sparkletron/righteous_tentacle_colecovision/pics/signals/analog/Q3_collector_at_idle_no_game.png

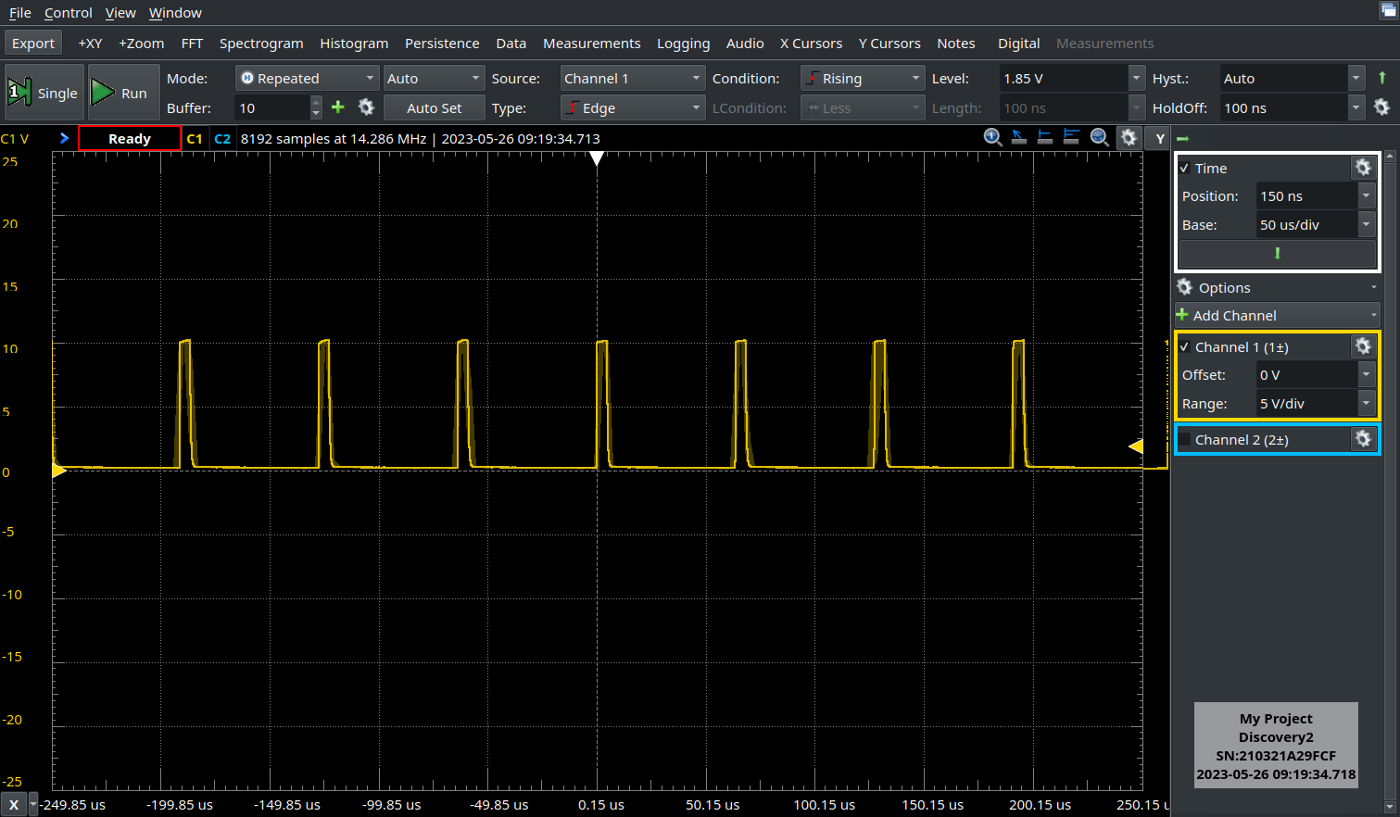
pics/signals/analog/Q3_collector_at_idle_no_game.png
