sparkletron/righteous_tentacle_colecovision/pics/signals/analog/rf_2_ac_at_idle_no_game.png

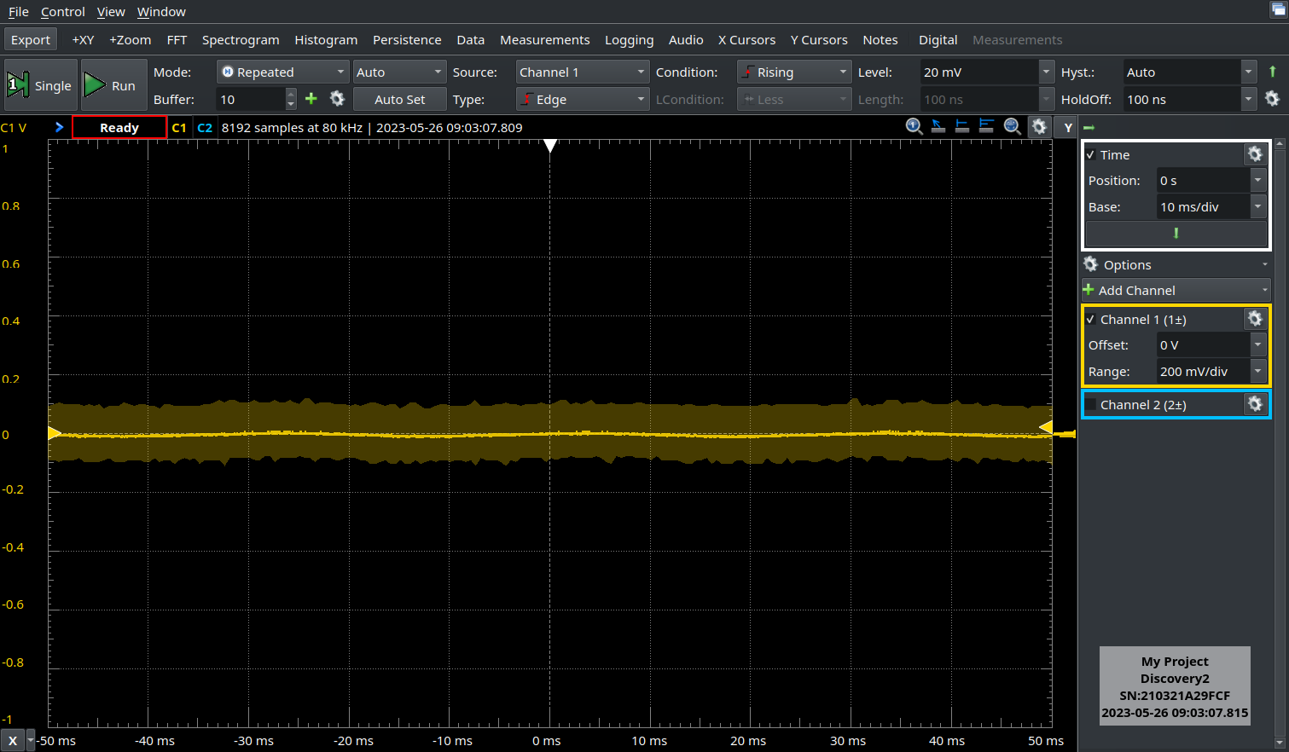
pics/signals/analog/rf_2_ac_at_idle_no_game.png
