sparkletron/righteous_tentacle_colecovision/pics/signals/analog/rf_7_Yb_ac_at_idle_no_game.png

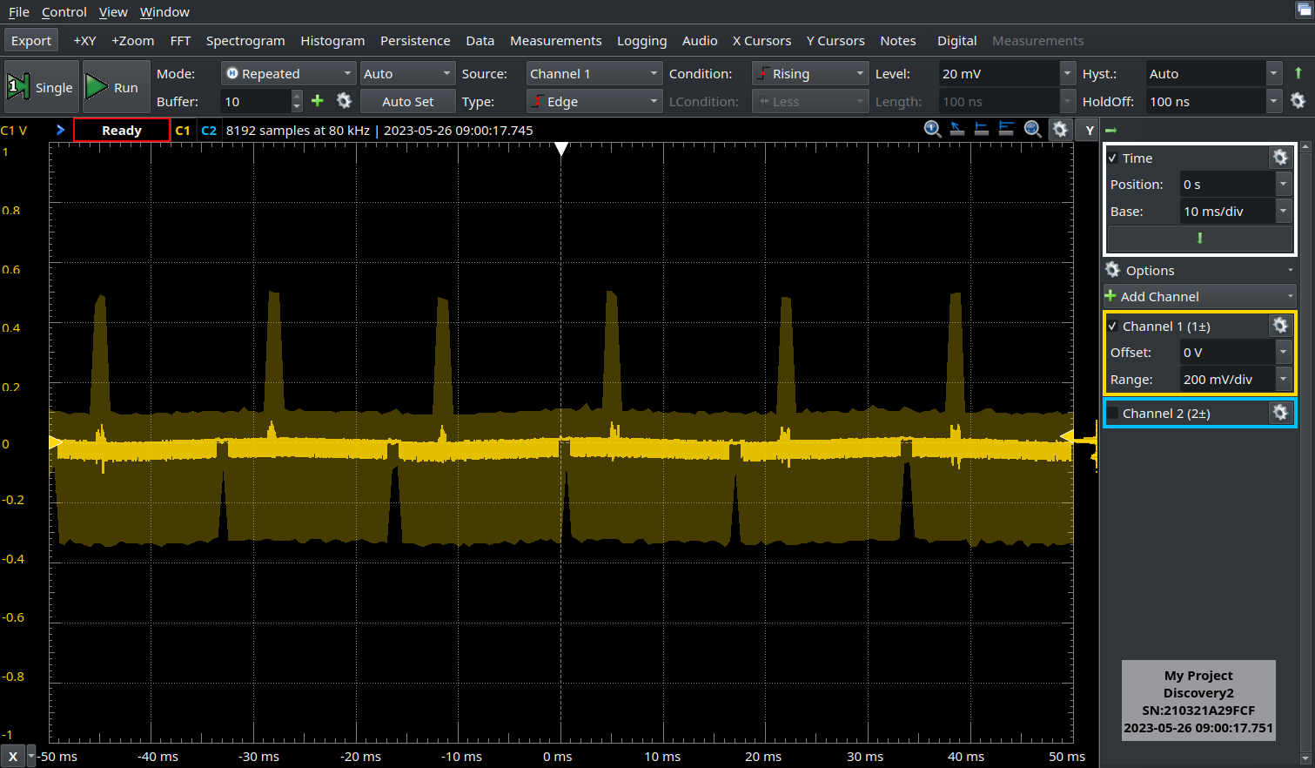
pics/signals/analog/rf_7_Yb_ac_at_idle_no_game.png
