sparkletron/righteous_tentacle_colecovision/pics/signals/analog/u7_1_A1_at_idle_no_game.png

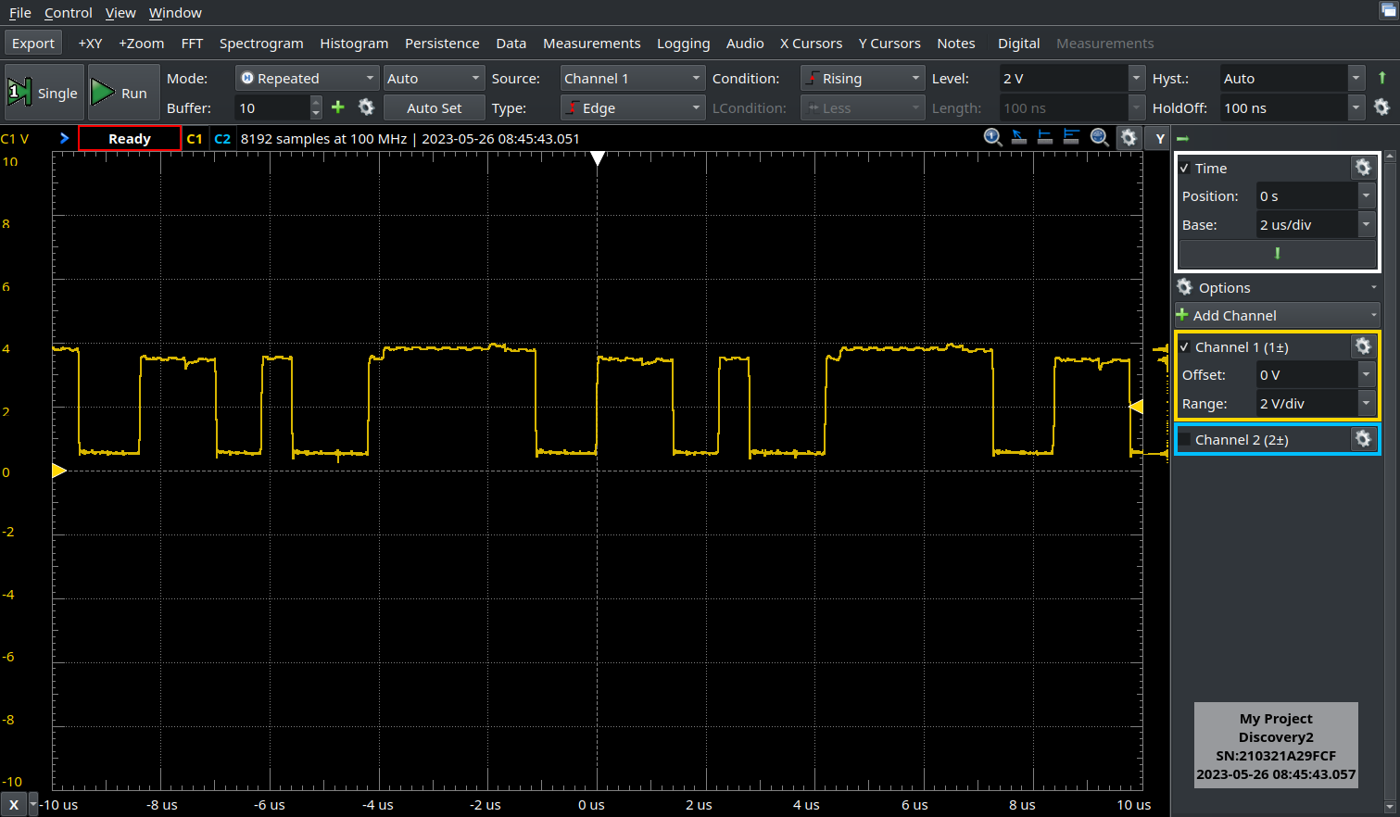
pics/signals/analog/u7_1_A1_at_idle_no_game.png
