sparkletron/righteous_tentacle_colecovision/pics/signals/analog/u7_4_wait_at_idle_no_game.png

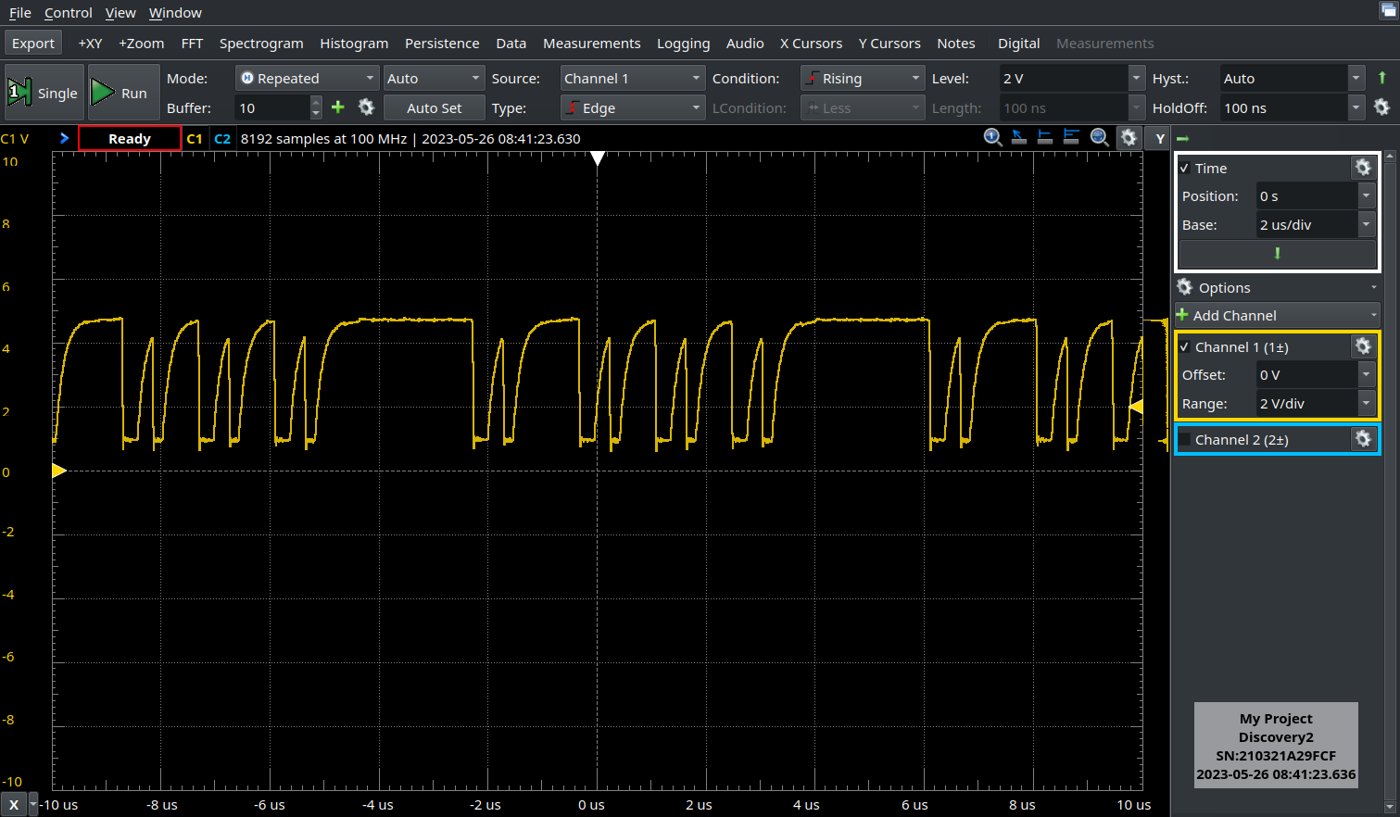
pics/signals/analog/u7_4_wait_at_idle_no_game.png
