sparkletron/righteous_tentacle_colecovision/pics/signals/analog/u22_3_2_at_idle_no_game.png

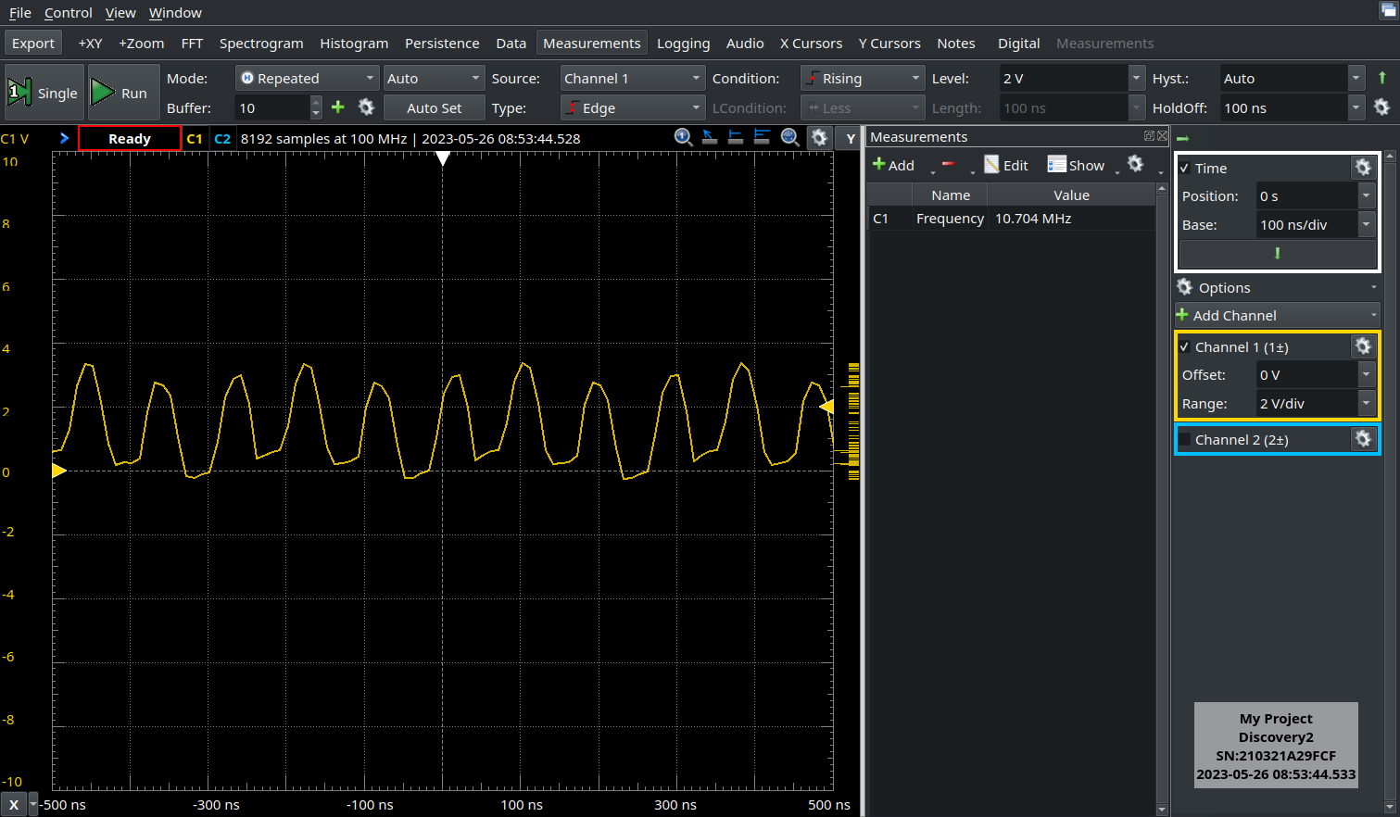
pics/signals/analog/u22_3_2_at_idle_no_game.png
