sparkletron/righteous_tentacle_colecovision/pics/signals/analog/u22_8_at_idle_no_game.png

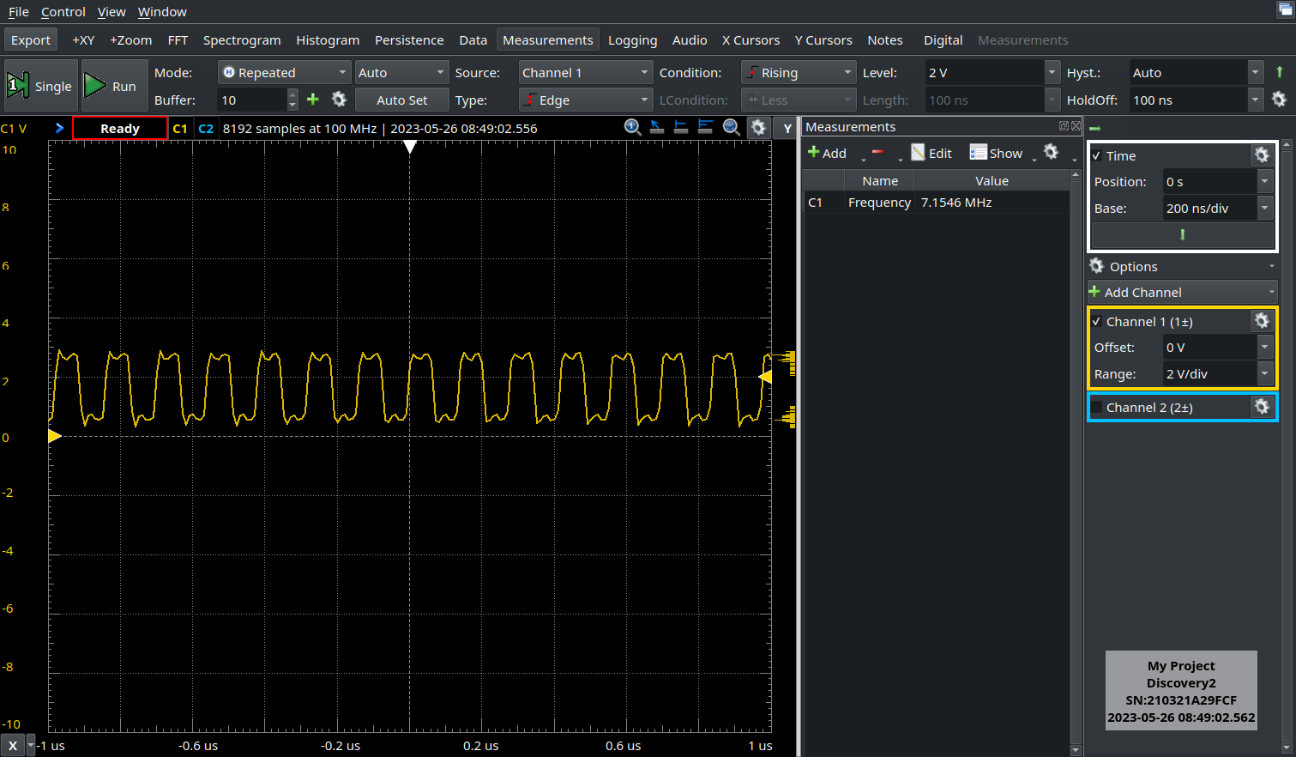
pics/signals/analog/u22_8_at_idle_no_game.png
