sparkletron/righteous_tentacle_colecovision/pics/signals/analog/VDP_ad_at_idle_no_game.png

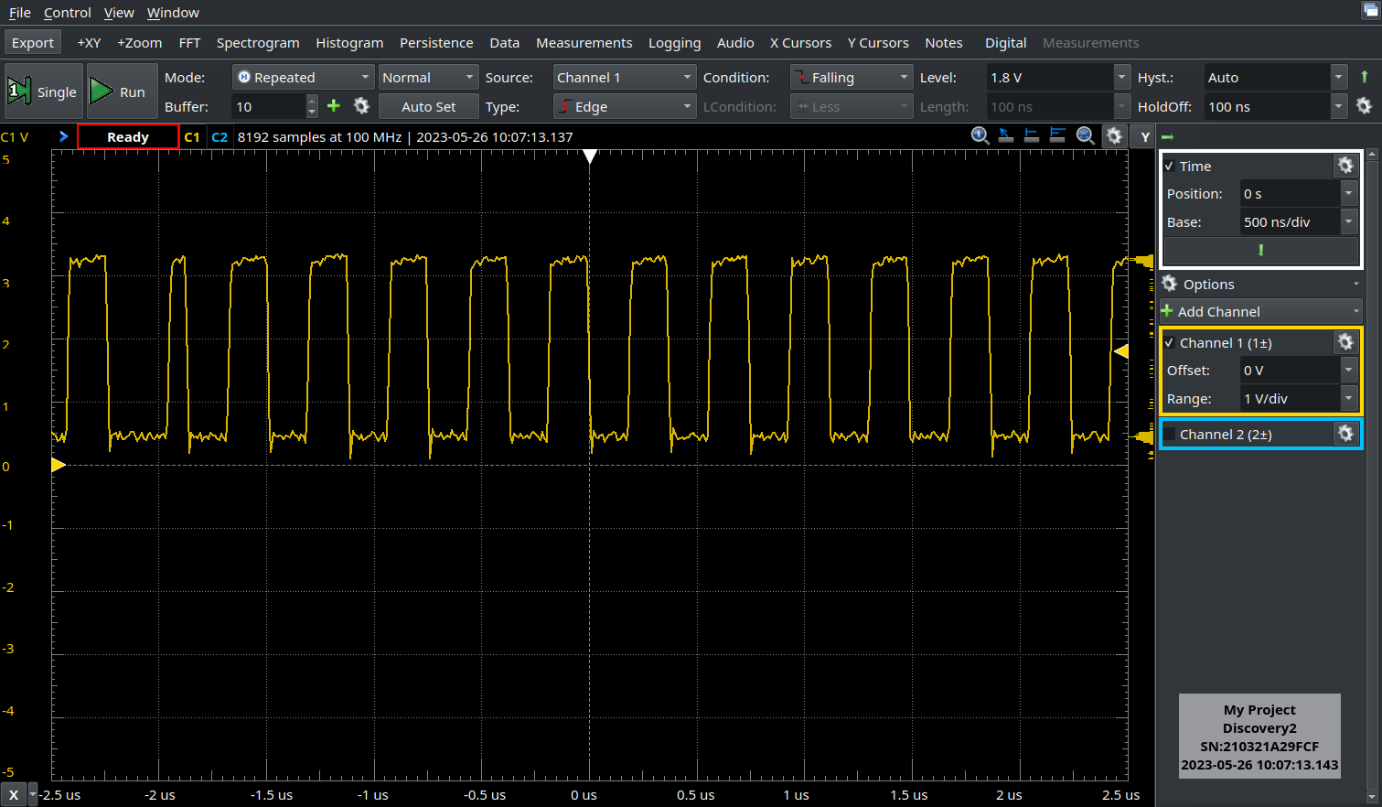
pics/signals/analog/VDP_ad_at_idle_no_game.png
