sparkletron/righteous_tentacle_colecovision/pics/signals/analog/VDP_csw_at_startup_no_game.png

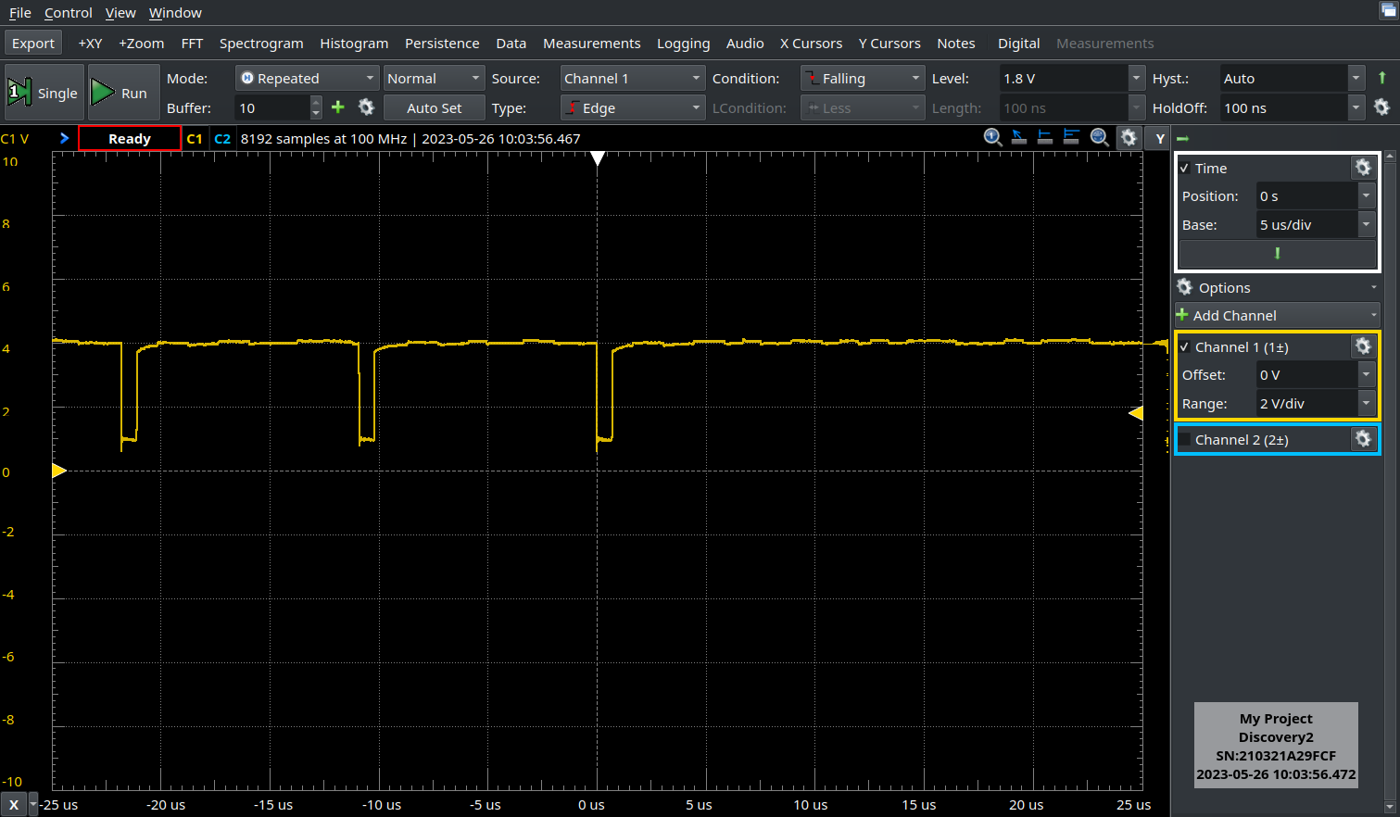
pics/signals/analog/VDP_csw_at_startup_no_game.png
