sparkletron/righteous_tentacle_colecovision/pics/signals/analog/z80_halt_at_idle_no_game.png

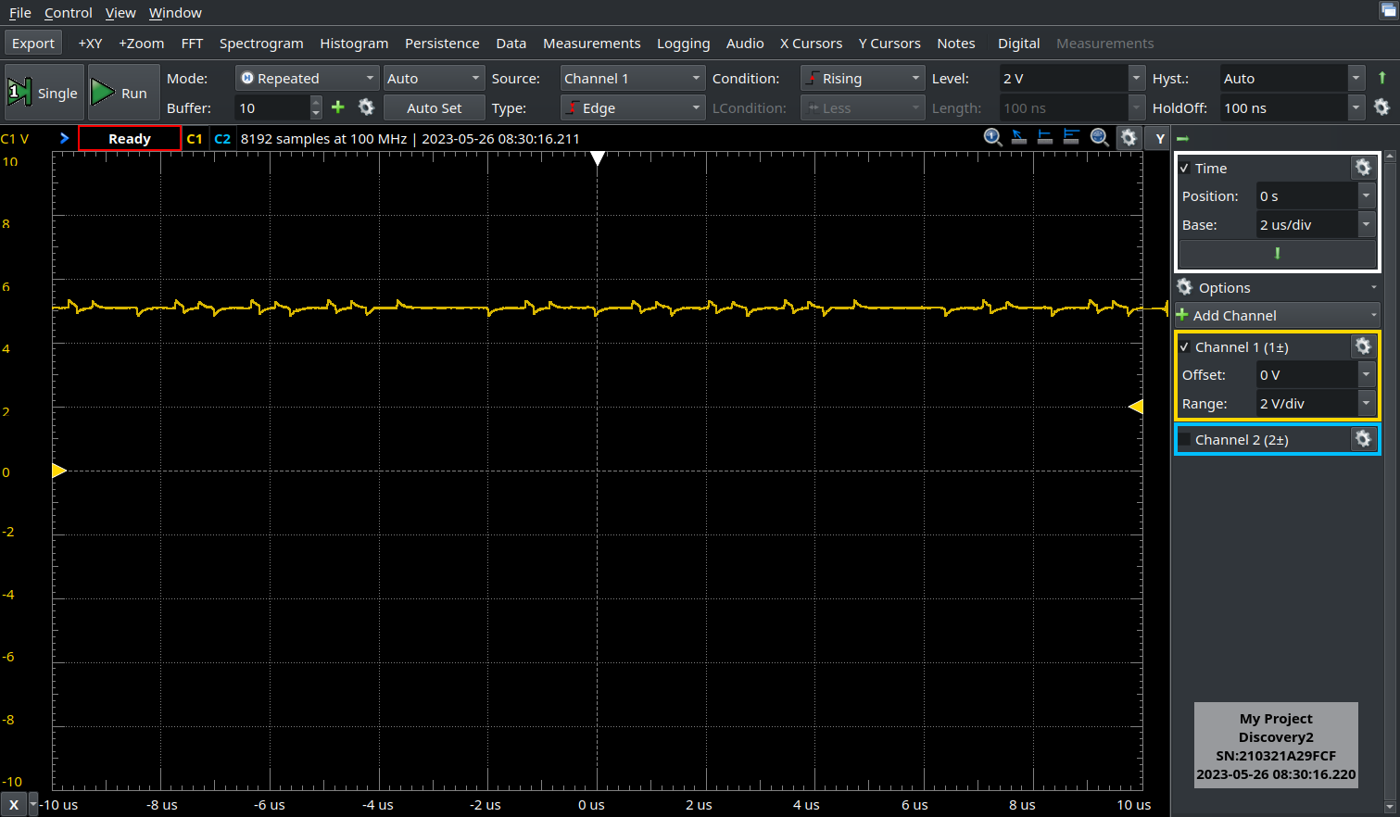
pics/signals/analog/z80_halt_at_idle_no_game.png
