sparkletron/righteous_tentacle_colecovision/pics/signals/analog/z80_reset_at_idle_no_game.png

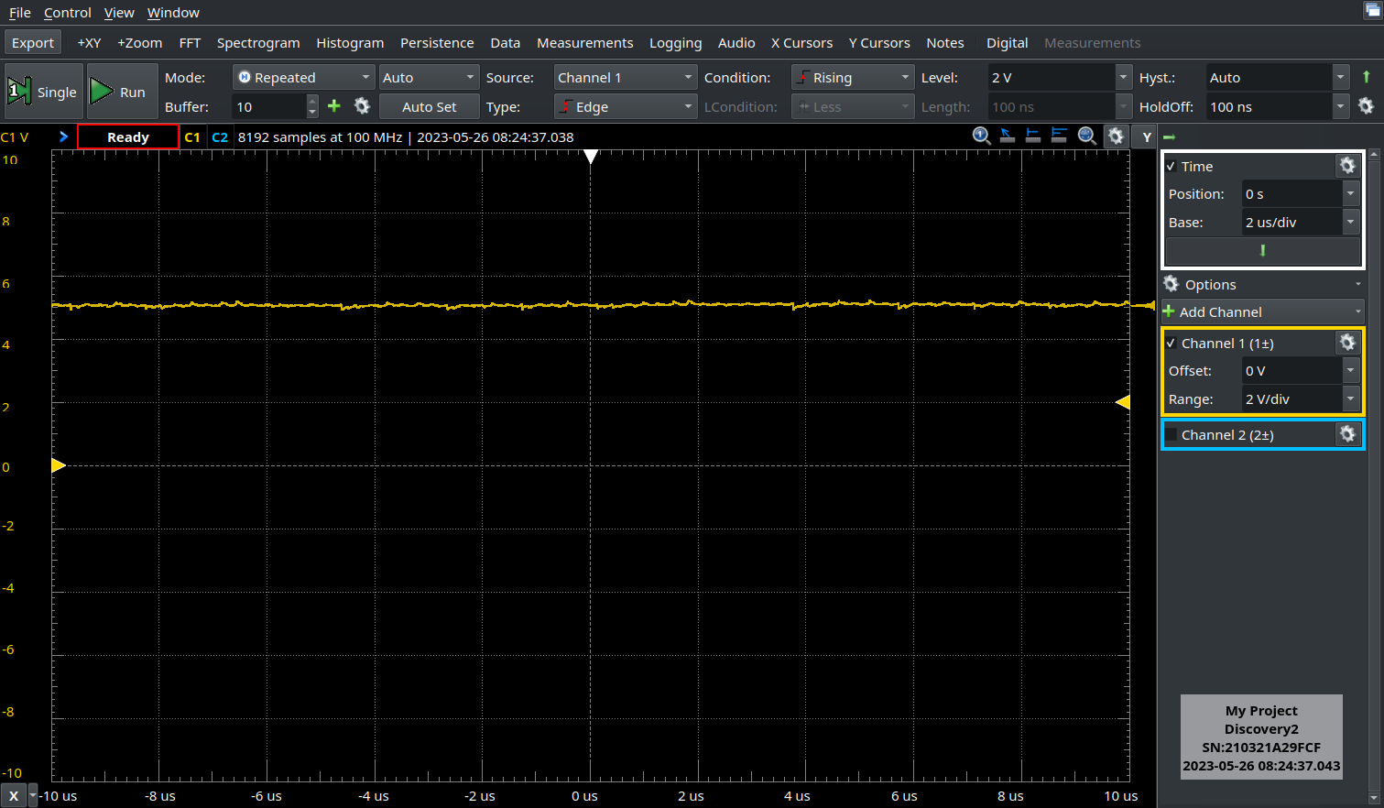
pics/signals/analog/z80_reset_at_idle_no_game.png
