sparkletron/righteous_tentacle_colecovision/pics/signals/digital/ram_data_cs_we_during_boot_no_game.png

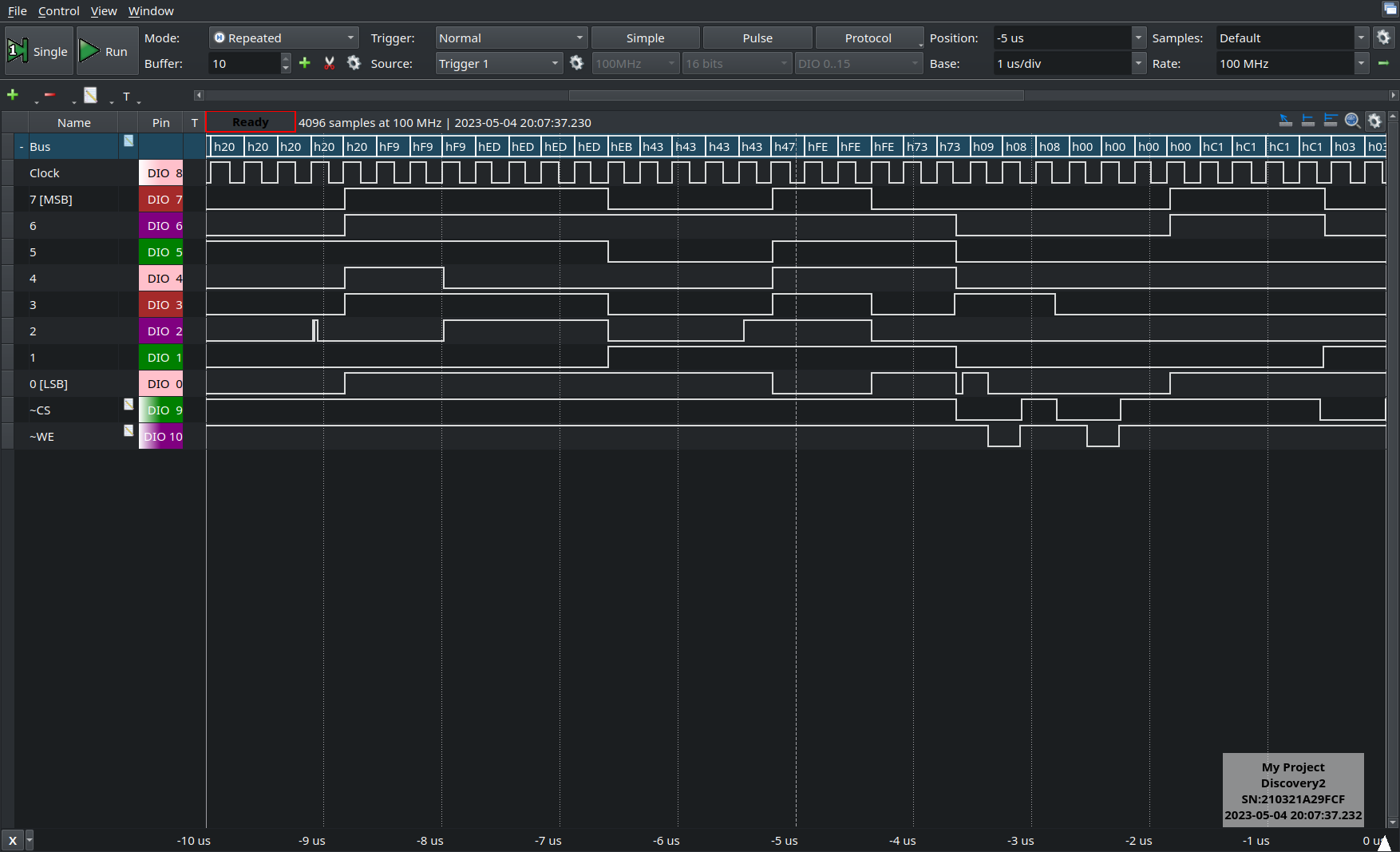
pics/signals/digital/ram_data_cs_we_during_boot_no_game.png
