sparkletron/righteous_tentacle_colecovision/pics/signals/digital/rom_data_ce_oe_at_idle_no_game.png

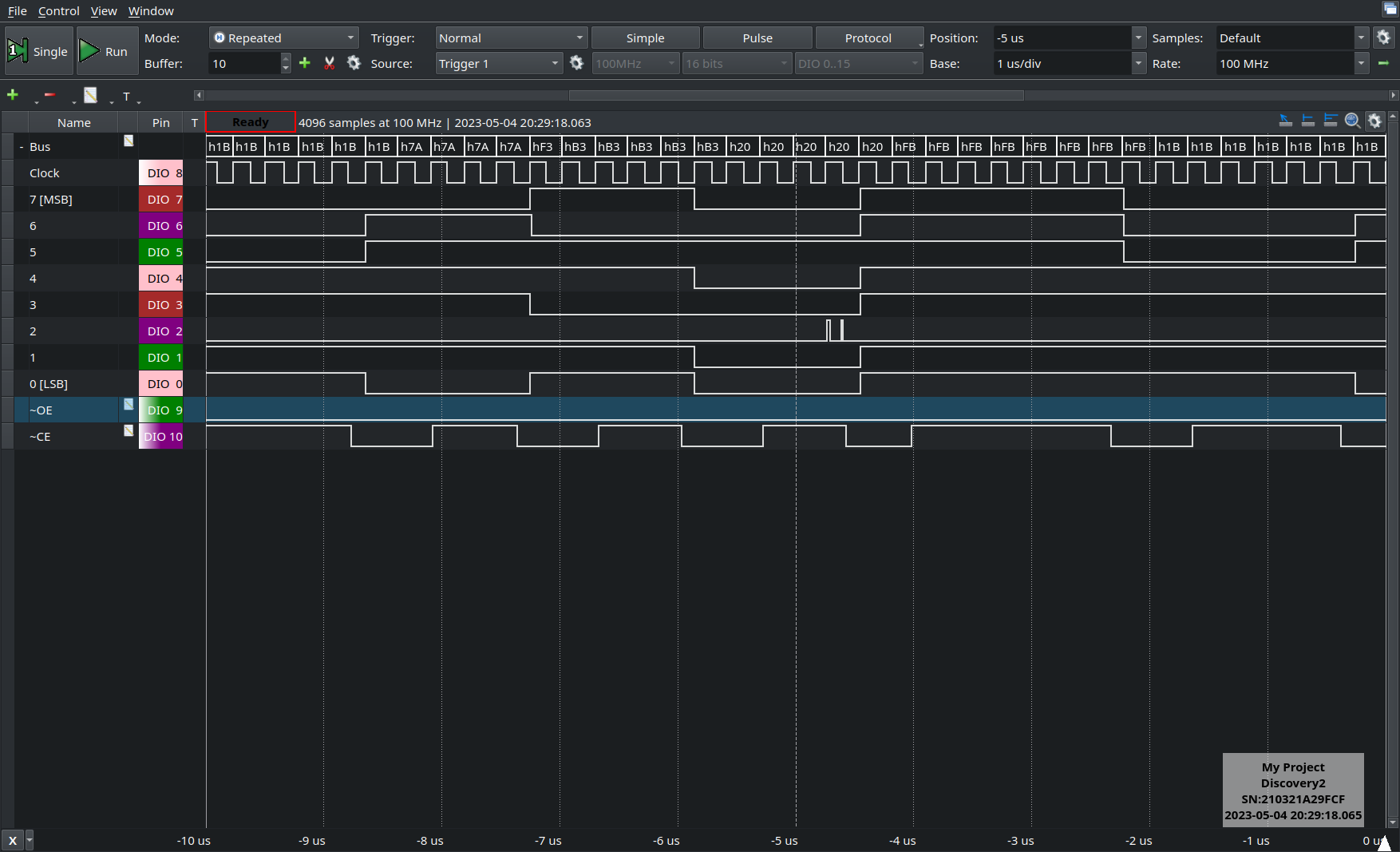
pics/signals/digital/rom_data_ce_oe_at_idle_no_game.png
