sparkletron/righteous_tentacle_colecovision/pics/signals/digital/z80_data_bus_at_idle_no_game.png

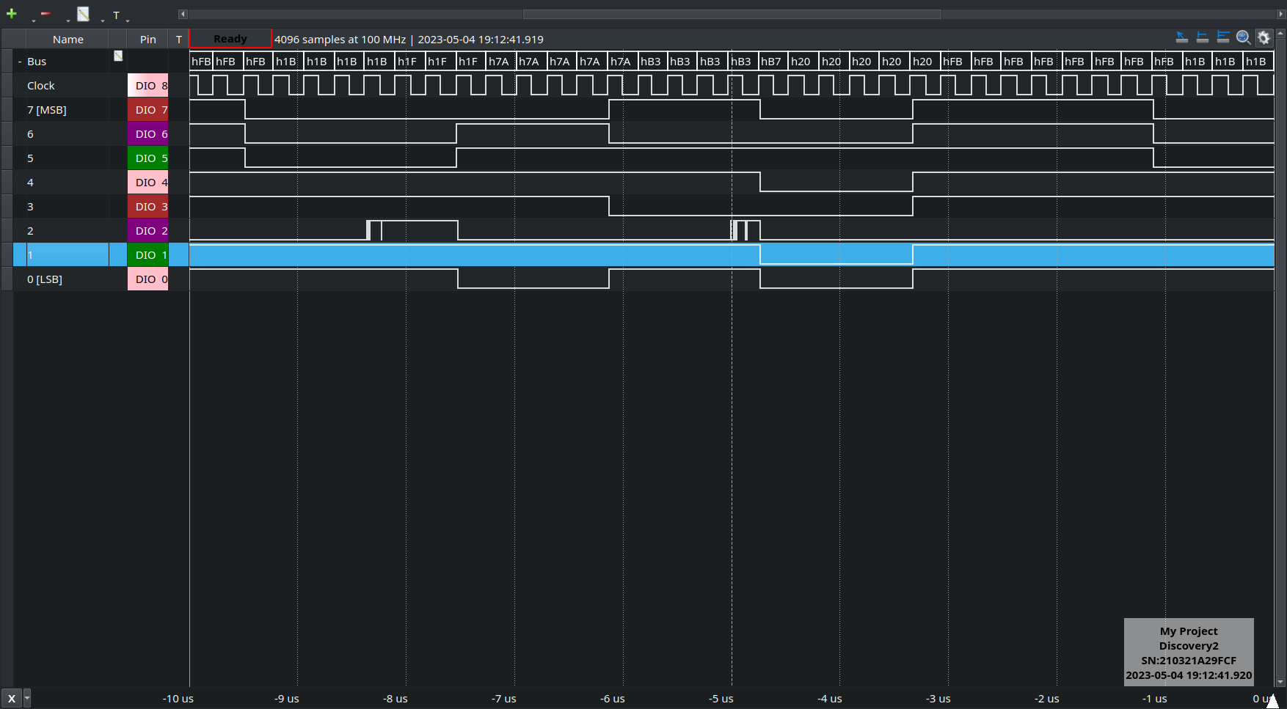
pics/signals/digital/z80_data_bus_at_idle_no_game.png
